sirknival/lichtsteuerung/img/Controlpanel_Back.jpg

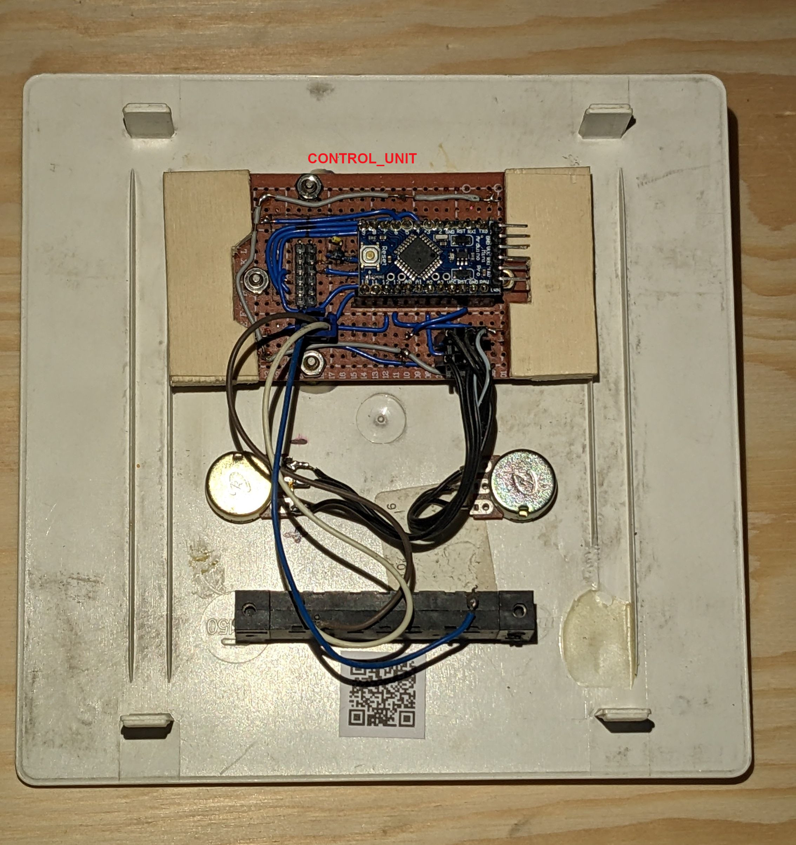
img/Controlpanel_Back.jpg
