sirknival/lichtsteuerung/img/Controlpanel_Front.jpg

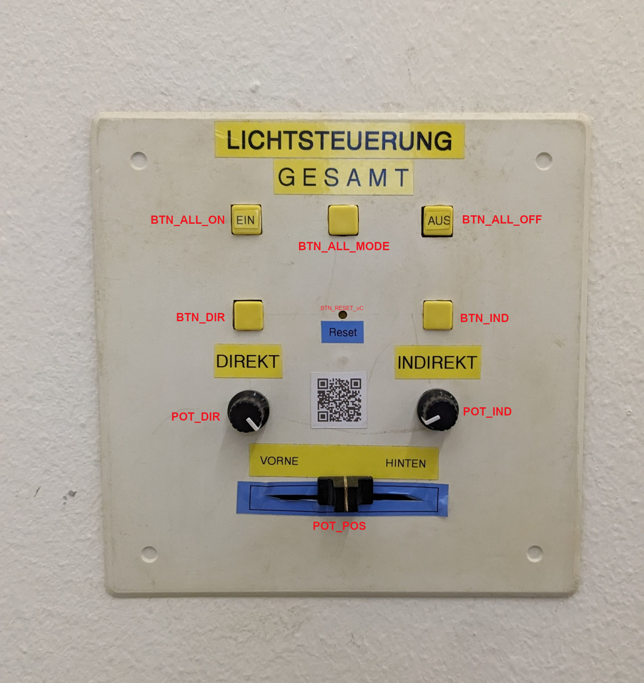
img/Controlpanel_Front.jpg
