sirknival/lichtsteuerung/schematics/Lichtsteuerung.sch

## EAGLE design schematics/Lichtsteuerung.sch (2020-03-24)

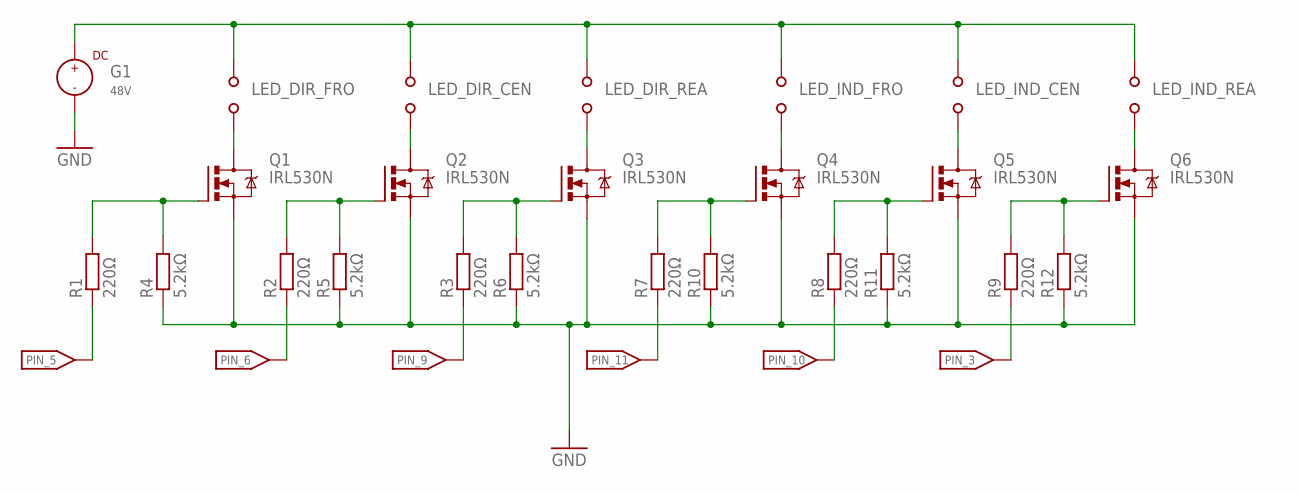
[picture p10: schematic Lichtsteuerung.sch]

Parts:
G1: 48V; TEMP_2
Q1, Q2, Q3, Q4, Q5, Q6: IRL530N; TO220BV
R1, R2, R3, R7, R8, R9: 220Ω; 0204V
R4, R5, R6, R10, R11, R12: 5.2kΩ; 0204V

Connections:
unnamed: Q1.S, Q2.S, Q3.S, Q4.S, Q5.S, Q6.S, R4.1, R5.1, R6.1, R10.1, R11.1, R12.1
unnamed: Q1.G, R1.2, R4.2
unnamed: Q2.G, R2.2, R5.2
unnamed: Q3.G, R3.2, R6.2
unnamed: Q4.G, R7.2, R10.2
unnamed: Q5.G, R8.2, R11.2
unnamed: Q6.G, R9.2, R12.2
