sirknival/lichtsteuerung/schematics/Lichtsteuerung_ControlUnit.sch

## EAGLE design schematics/Lichtsteuerung_ControlUnit.sch (2022-12-21)

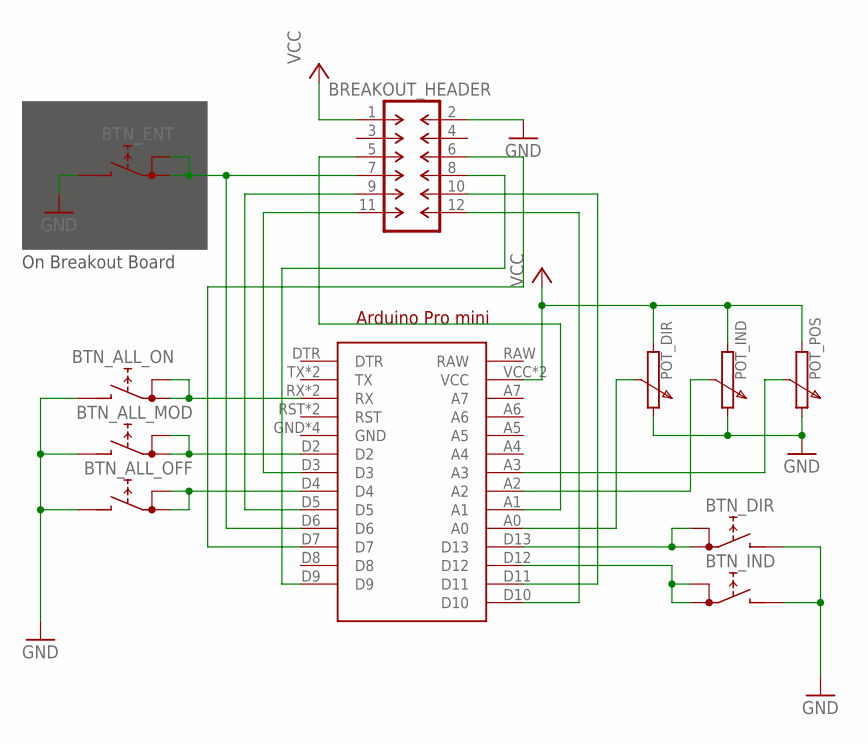
[picture p11: schematic Lichtsteuerung_ControlUnit.sch]

Parts:
ARDUINO1: 1; ARDUINO_PRO_MINI
BREAKOUT_HEADER: M-2X06-DIL-2MM_M; DIL-2MM-2X06_M
BTN_ALL_MOD: RDT1034
BTN_ALL_OFF: RDT1034
BTN_ALL_ON: RDT1034
BTN_DIR: RDT1034
BTN_ENT: RDT1034
BTN_IND: RDT1034

Connections:
GND: BREAKOUT_HEADER.2, BTN_ALL_MOD.B, BTN_ALL_OFF.B, BTN_ALL_ON.B, BTN_DIR.B, BTN_ENT.B, BTN_IND.B
unnamed: ARDUINO1.D2, BTN_ALL_MOD.A, BTN_ALL_MOD.A1
unnamed: ARDUINO1.RX, BTN_ALL_ON.A, BTN_ALL_ON.A1
unnamed: ARDUINO1.D4, BTN_ALL_OFF.A, BTN_ALL_OFF.A1
unnamed: ARDUINO1.D12, BTN_IND.A, BTN_IND.A1
unnamed: ARDUINO1.D13, BTN_DIR.A, BTN_DIR.A1
unnamed: ARDUINO1.A1, BREAKOUT_HEADER.5
unnamed: ARDUINO1.D7, BREAKOUT_HEADER.6
unnamed: ARDUINO1.D6, BREAKOUT_HEADER.7, BTN_ENT.A, BTN_ENT.A1
unnamed: ARDUINO1.D5, BREAKOUT_HEADER.9
unnamed: ARDUINO1.D3, BREAKOUT_HEADER.11
unnamed: ARDUINO1.D9, BREAKOUT_HEADER.8
unnamed: ARDUINO1.D11, BREAKOUT_HEADER.10
unnamed: ARDUINO1.D10, BREAKOUT_HEADER.12
VCC: ARDUINO1.VCC, BREAKOUT_HEADER.1

Notes on the sheet:
POT_DIR
POT_IND
POT_POS
On Breakout Board
