sirknival/lichtsteuerung/schematics/Vent_BreakoutBord.sch

## EAGLE design schematics/Vent_BreakoutBord.sch (2022-12-26)

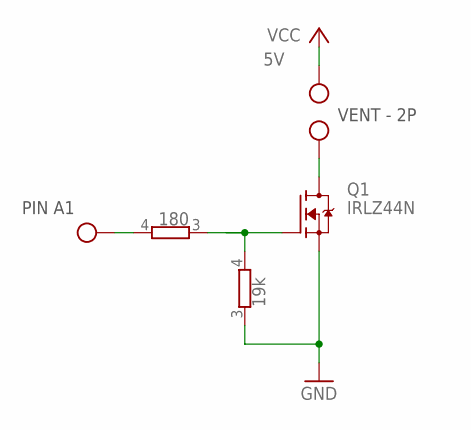
[picture p12: schematic Vent_BreakoutBord.sch]

Parts:
Q1: IRLZ44N; TO254P1054X469X1930-3
RN1: 19k; SIL4
RN2: 180; SIL4

Connections:
GND: Q1.3 (S), RN1.3 (1)
unnamed: Q1.1 (G), RN1.4 (2), RN2.3 (1)
VCC: Q1.2 (D), RN2.4 (2)

Notes on the sheet:
VENT - 2P
PIN A1
